facebookresearch/pando/pcbs/RemoteIMU/Documentation/hdmi_connector.png

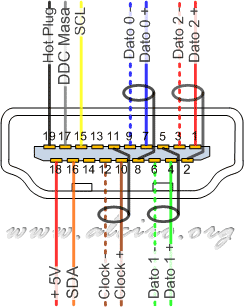
pcbs/RemoteIMU/Documentation/hdmi_connector.png
