facebookresearch/pando/software/python/visualizations/bci/stimulus/psychopy/images/files/cuff.png

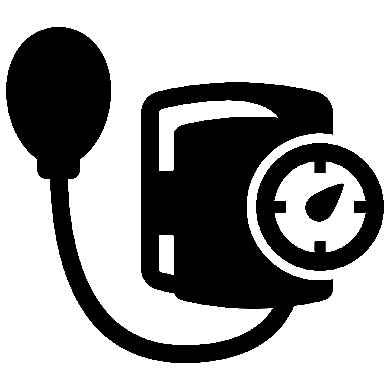
software/python/visualizations/bci/stimulus/psychopy/images/files/cuff.png
