facebookresearch/pando/software/python/visualizations/bci/stimulus/psychopy/images/files/deep_breaths.png

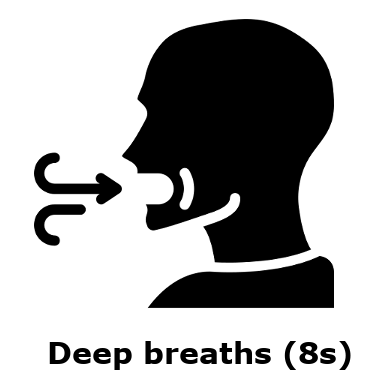
software/python/visualizations/bci/stimulus/psychopy/images/files/deep_breaths.png
