facebookresearch/pando/software/python/visualizations/bci/stimulus/psychopy/images/files/foot_left.png

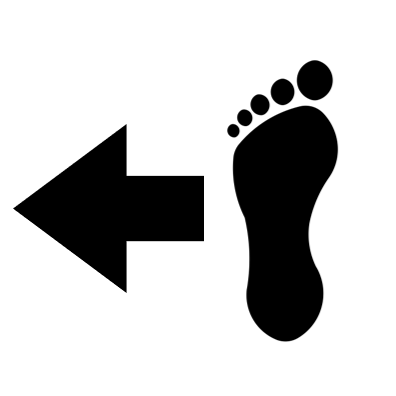
software/python/visualizations/bci/stimulus/psychopy/images/files/foot_left.png
