facebookresearch/pando/software/python/visualizations/bci/stimulus/psychopy/images/files/foot_right.png

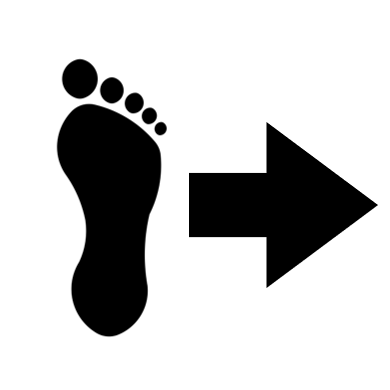
software/python/visualizations/bci/stimulus/psychopy/images/files/foot_right.png
