facebookresearch/pando/software/python/visualizations/bci/stimulus/psychopy/images/files/hand_left.png

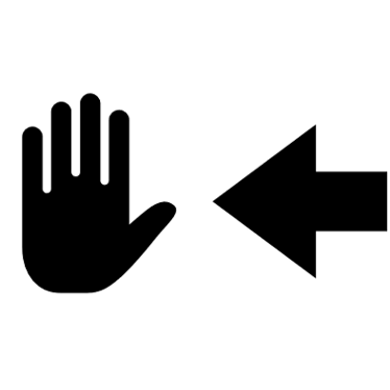
software/python/visualizations/bci/stimulus/psychopy/images/files/hand_left.png
