facebookresearch/pando/software/python/visualizations/bci/stimulus/psychopy/images/files/hand_right.png

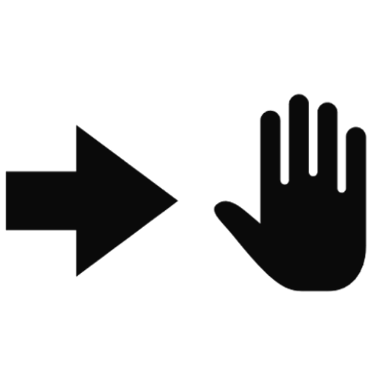
software/python/visualizations/bci/stimulus/psychopy/images/files/hand_right.png
