facebookresearch/pando/software/python/visualizations/bci/stimulus/psychopy/images/files/heart.png

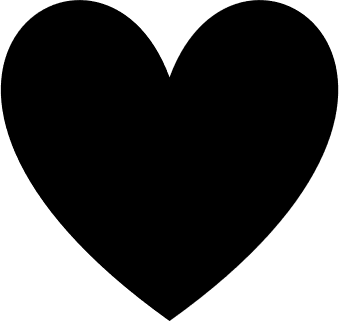
software/python/visualizations/bci/stimulus/psychopy/images/files/heart.png
