facebookresearch/pando/software/python/visualizations/bci/stimulus/psychopy/images/files/hold_breath.png

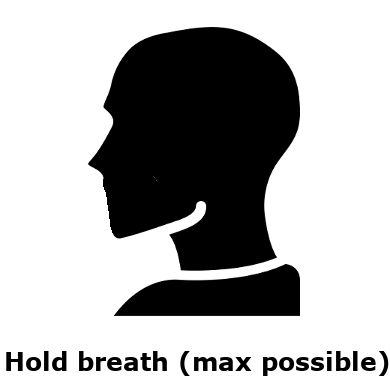
software/python/visualizations/bci/stimulus/psychopy/images/files/hold_breath.png
