facebookresearch/pando/software/python/visualizations/bci/stimulus/psychopy/images/files/left_arrow.png

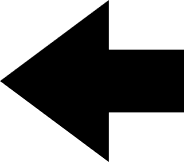
software/python/visualizations/bci/stimulus/psychopy/images/files/left_arrow.png
