facebookresearch/pando/software/python/visualizations/bci/stimulus/psychopy/images/files/left_hand_yaw.png

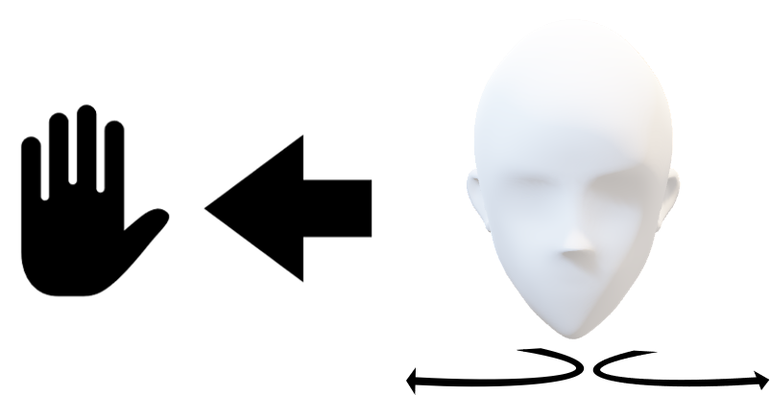
software/python/visualizations/bci/stimulus/psychopy/images/files/left_hand_yaw.png
