facebookresearch/pando/software/python/visualizations/bci/stimulus/psychopy/images/files/pitch_down.png

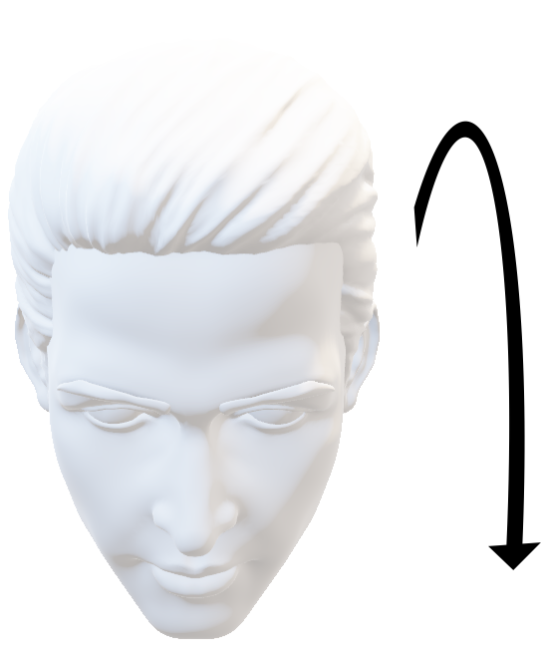
software/python/visualizations/bci/stimulus/psychopy/images/files/pitch_down.png
