facebookresearch/pando/software/python/visualizations/bci/stimulus/psychopy/images/files/right_arrow.png

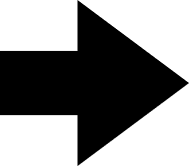
software/python/visualizations/bci/stimulus/psychopy/images/files/right_arrow.png
