facebookresearch/pando/software/python/visualizations/bci/stimulus/psychopy/images/files/right_hand_roll.png

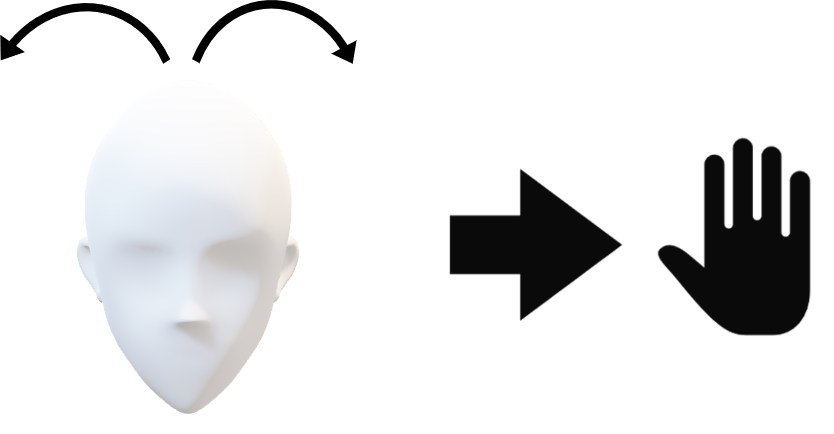
software/python/visualizations/bci/stimulus/psychopy/images/files/right_hand_roll.png
