facebookresearch/pando/software/python/visualizations/bci/stimulus/psychopy/images/files/roll_left.png

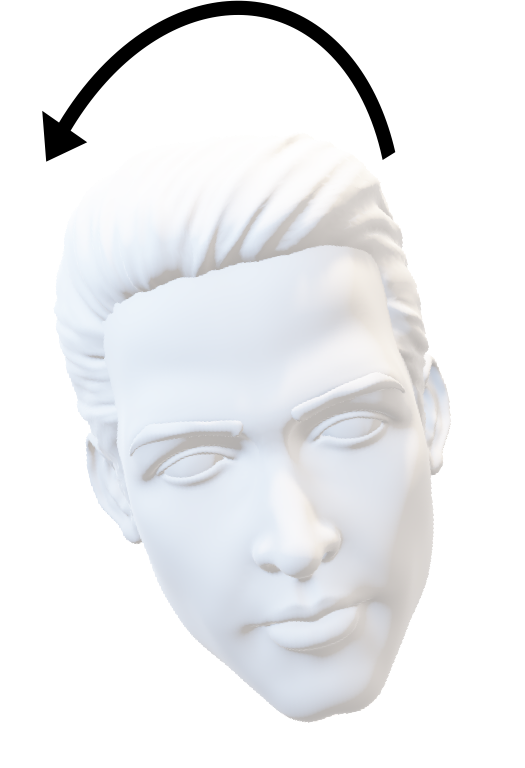
software/python/visualizations/bci/stimulus/psychopy/images/files/roll_left.png
