facebookresearch/pando/software/python/visualizations/bci/stimulus/psychopy/images/files/roll_right.png

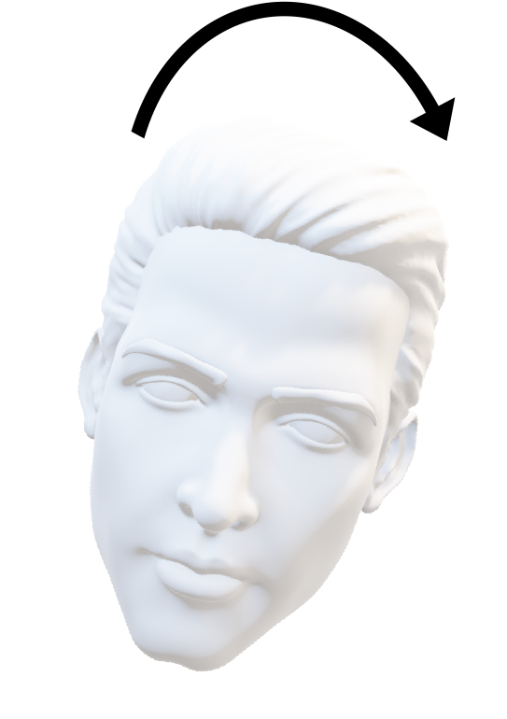
software/python/visualizations/bci/stimulus/psychopy/images/files/roll_right.png
