facebookresearch/pando/software/python/visualizations/bci/stimulus/psychopy/images/files/tongue.png

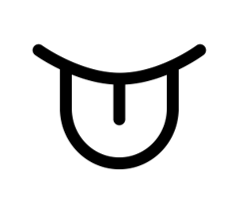
software/python/visualizations/bci/stimulus/psychopy/images/files/tongue.png
