facebookresearch/pando/software/python/visualizations/bci/stimulus/psychopy/images/files/yaw_left.png

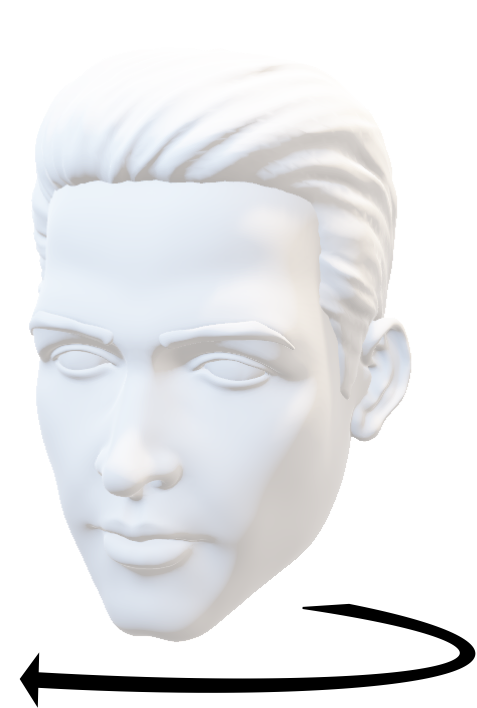
software/python/visualizations/bci/stimulus/psychopy/images/files/yaw_left.png
