facebookresearch/pando/software/python/visualizations/bci/stimulus/psychopy/images/files/yaw_right.png

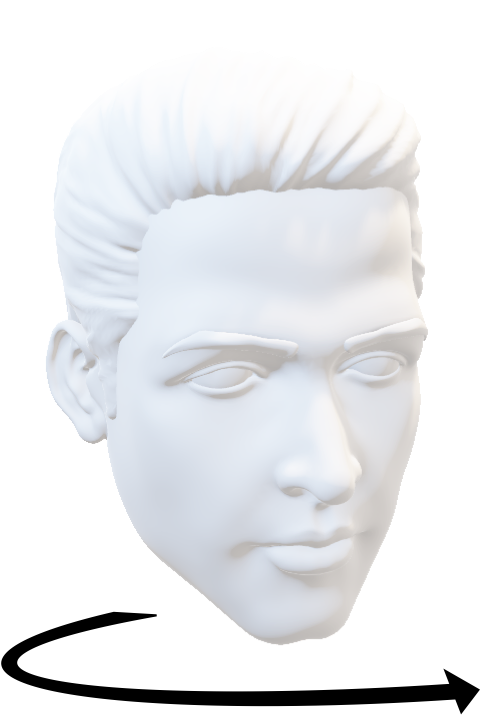
software/python/visualizations/bci/stimulus/psychopy/images/files/yaw_right.png
